kromych/fpga-vga/img/01.png

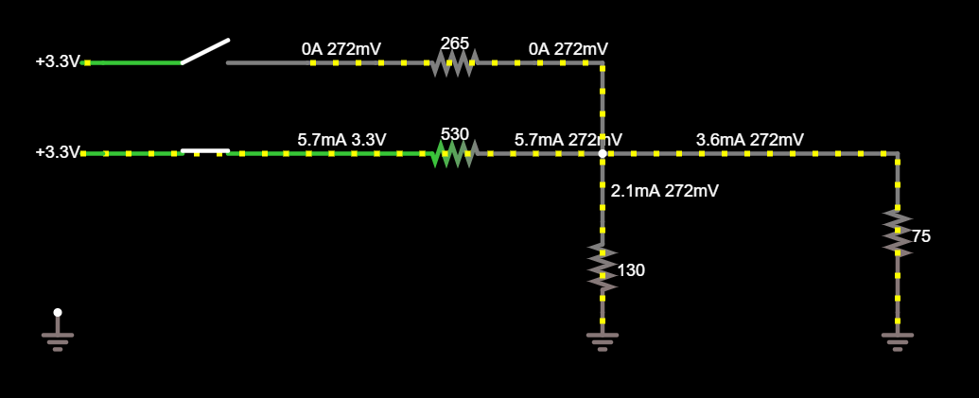
img/01.png
