kromych/fpga-vga/img/10.png

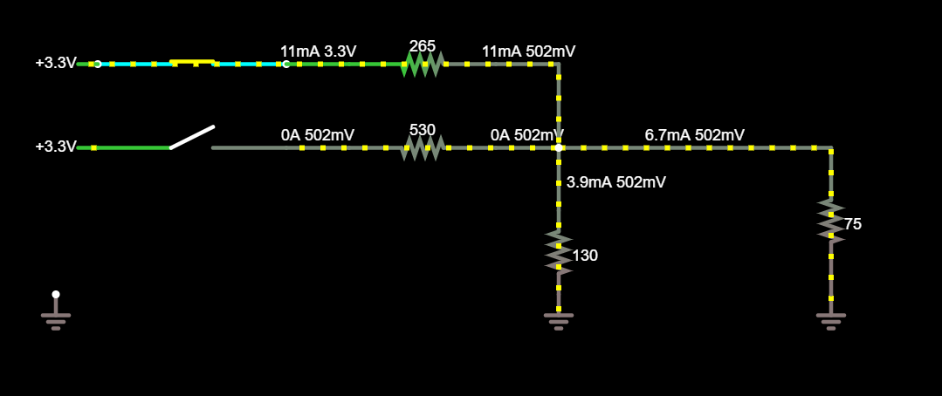
img/10.png
