kromych/fpga-vga/img/11.png

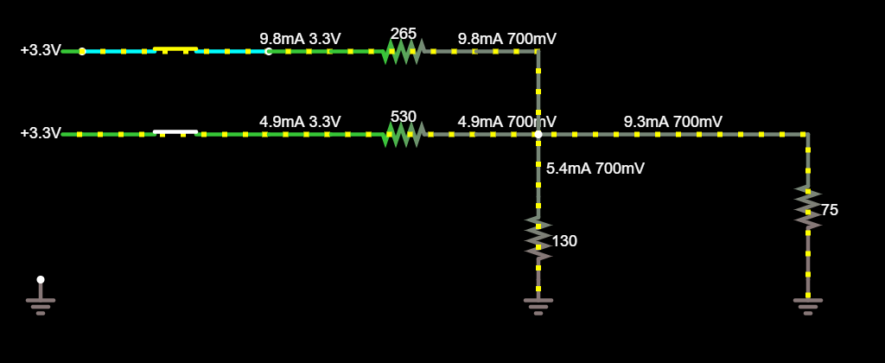
img/11.png
